carlosbanda01/Proyecto-GPS-MQTT/Diseños/Diseño_PCB/PCB_impresas/CBC_ver4.pdf

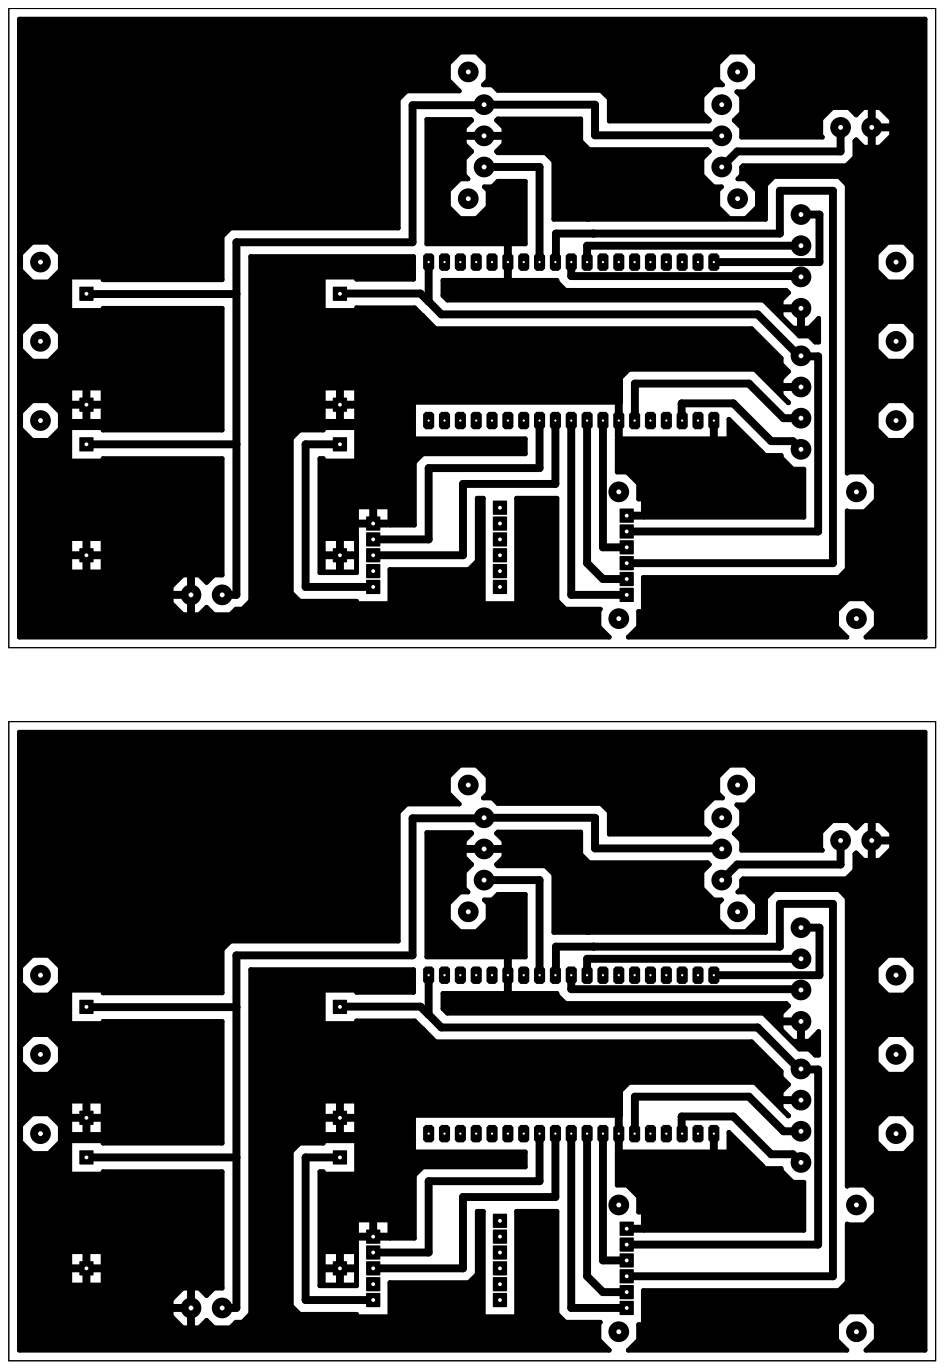
[picture p44: page 1]
