carlosbanda01/Proyecto-GPS-MQTT/Diseños/Diseño_PCB/PCB_impresas/CBC_ver4_info.pdf

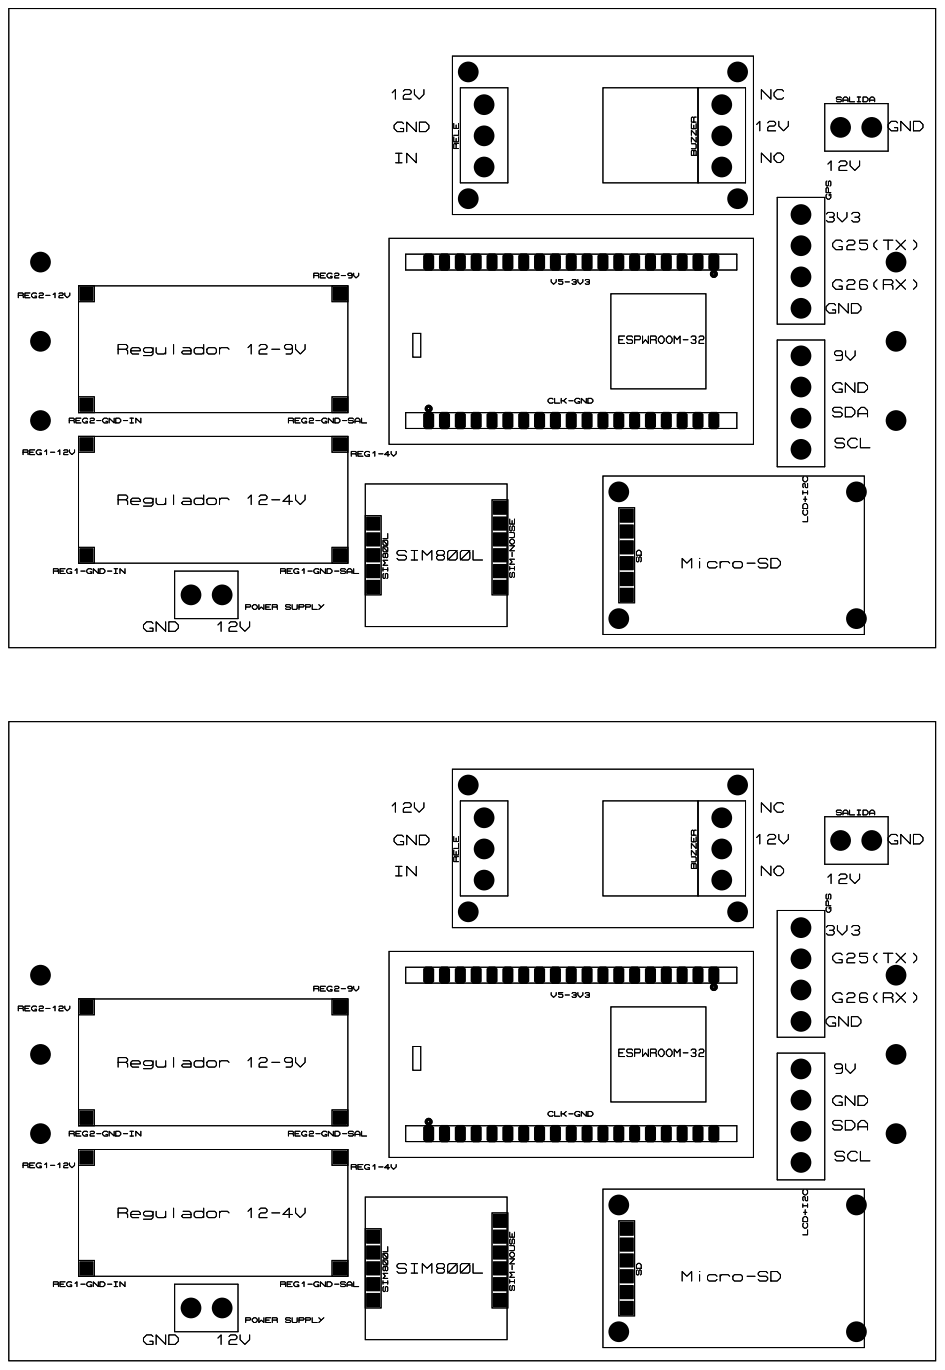
[picture p45: page 1]
